SaifSabban/N64-WirelessControllerMod/Extra/Images/5.jpg

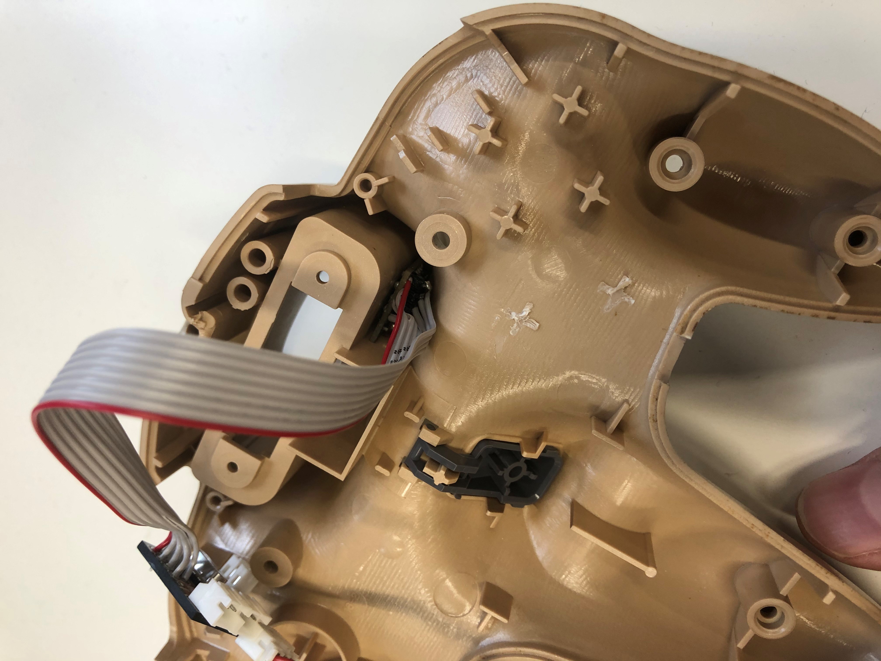
Extra/Images/5.jpg
