SaifSabban/N64-WirelessControllerMod/Extra/Images/6.jpg

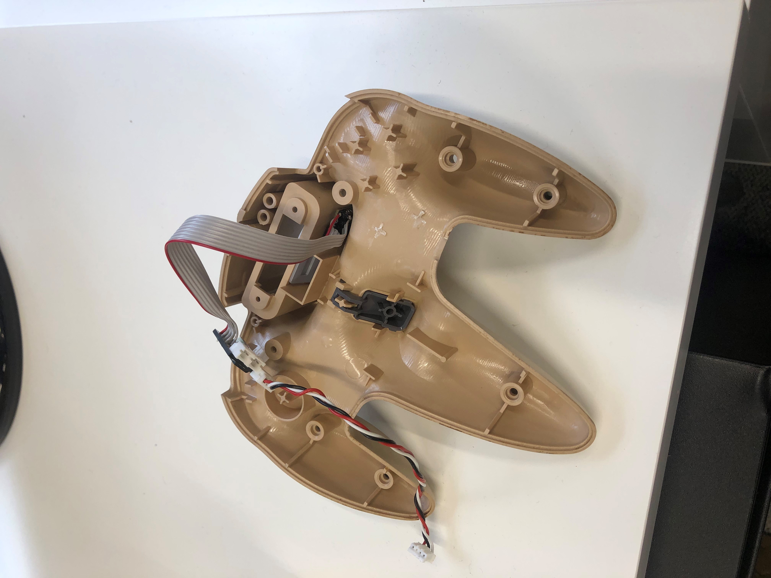
Extra/Images/6.jpg
