SaifSabban/N64-WirelessControllerMod/Extra/Images/10.jpg

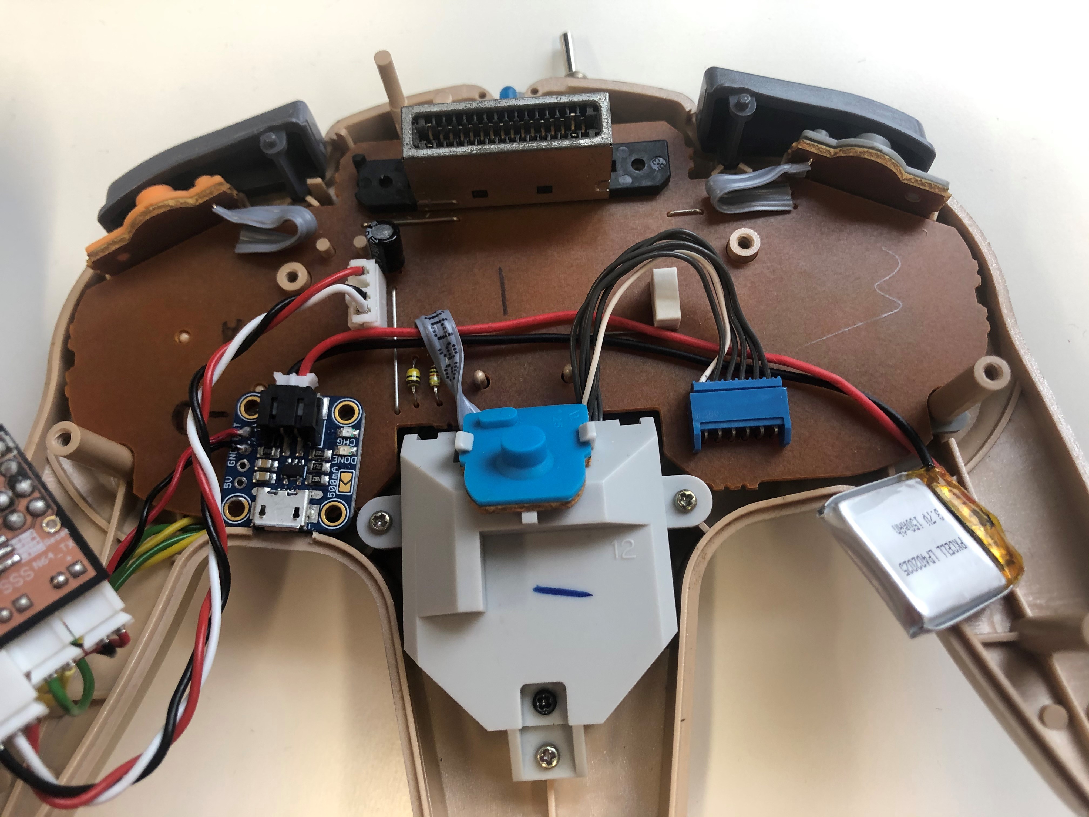
Extra/Images/10.jpg
