SaifSabban/N64-WirelessControllerMod/Extra/Images/12.jpg

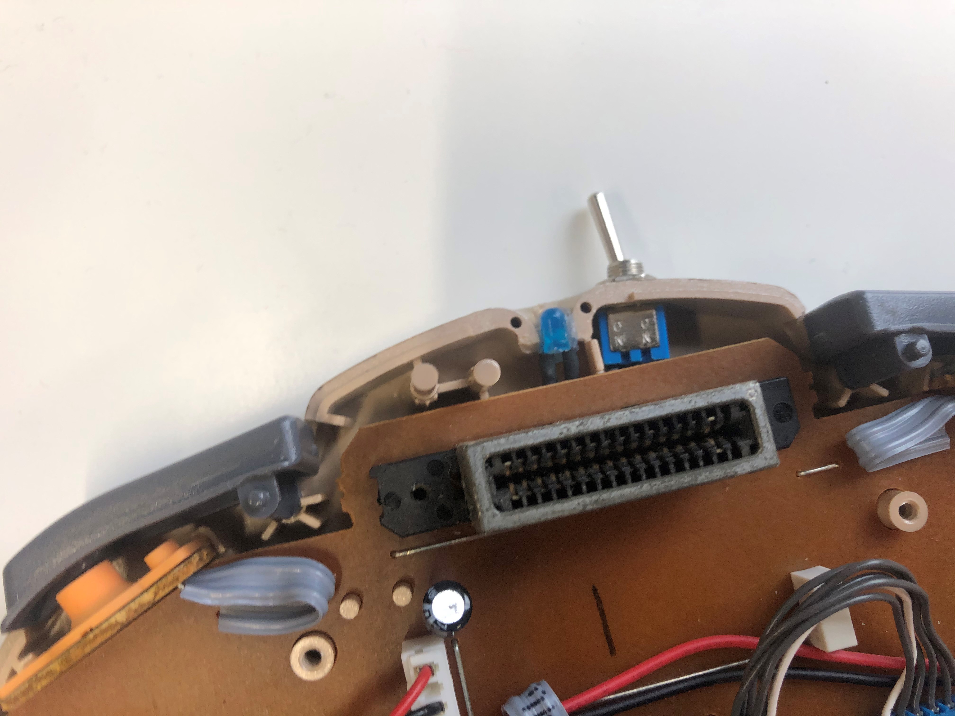
Extra/Images/12.jpg
