SaifSabban/N64-WirelessControllerMod/Extra/Images/13.jpg

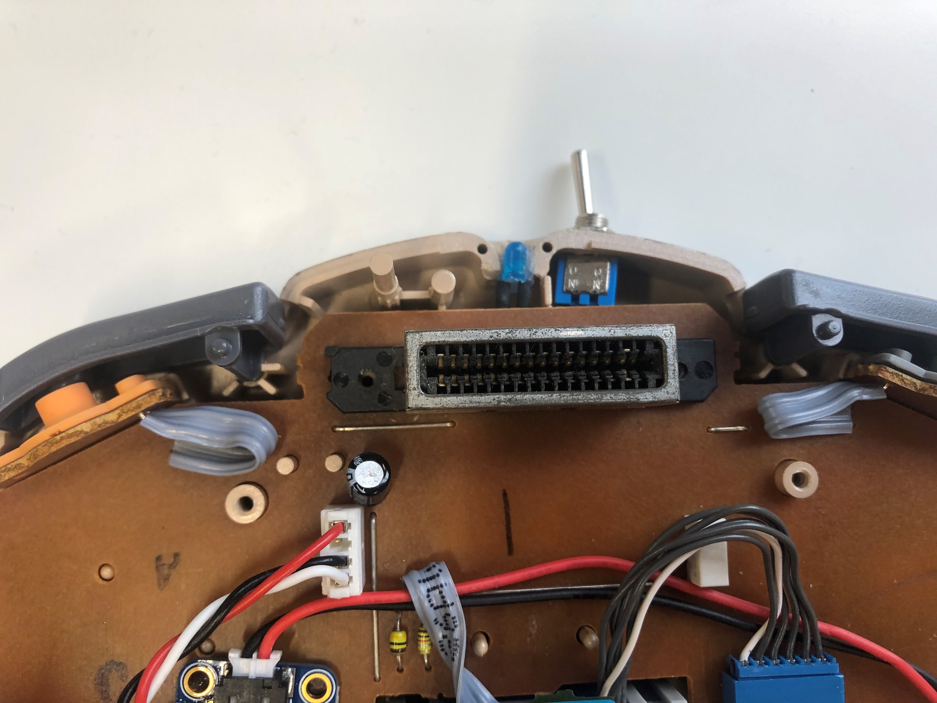
Extra/Images/13.jpg
