SaifSabban/N64-WirelessControllerMod/Extra/Images/14.jpg

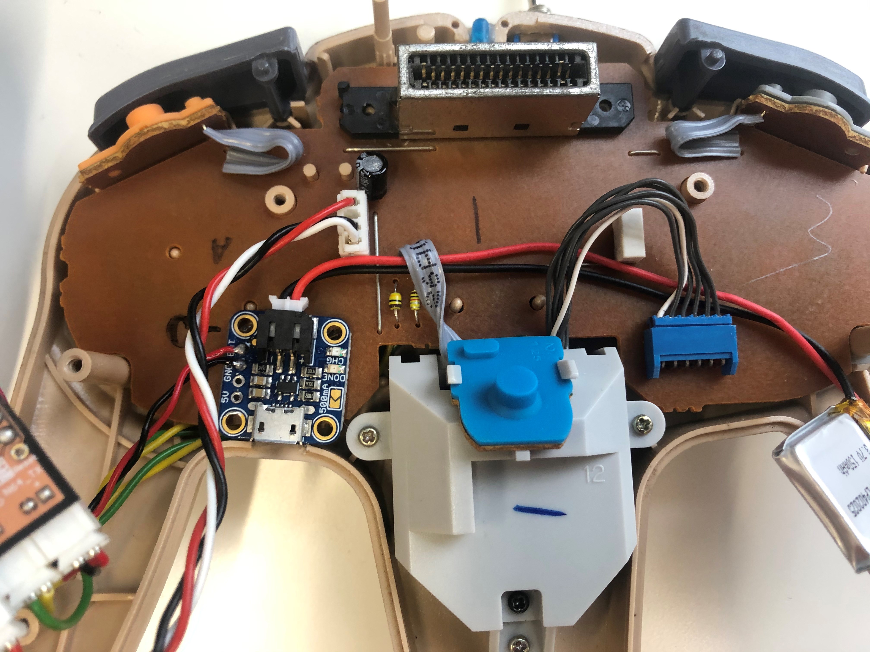
Extra/Images/14.jpg
