SaifSabban/N64-WirelessControllerMod/Extra/Images/17.jpg

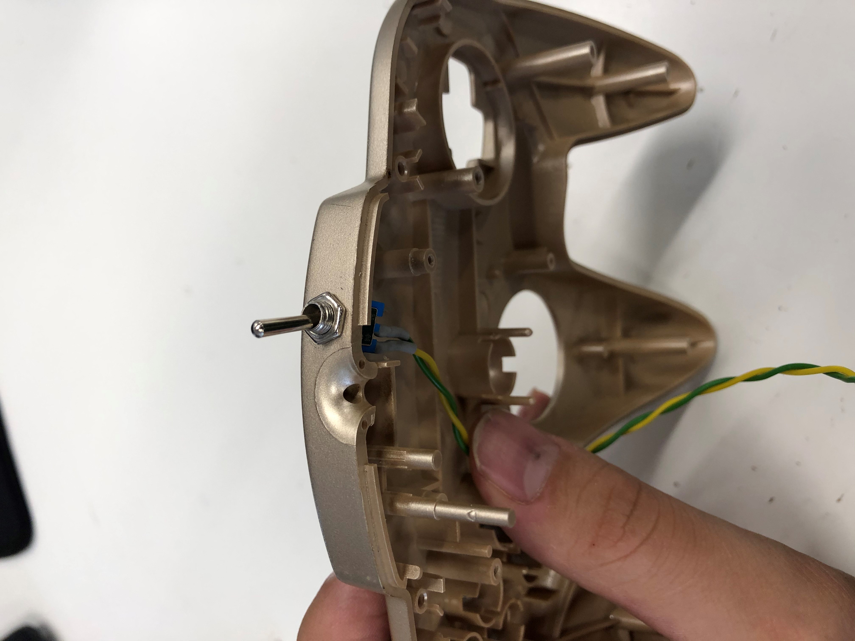
Extra/Images/17.jpg
