SaifSabban/N64-WirelessControllerMod/Extra/Images/19.jpg

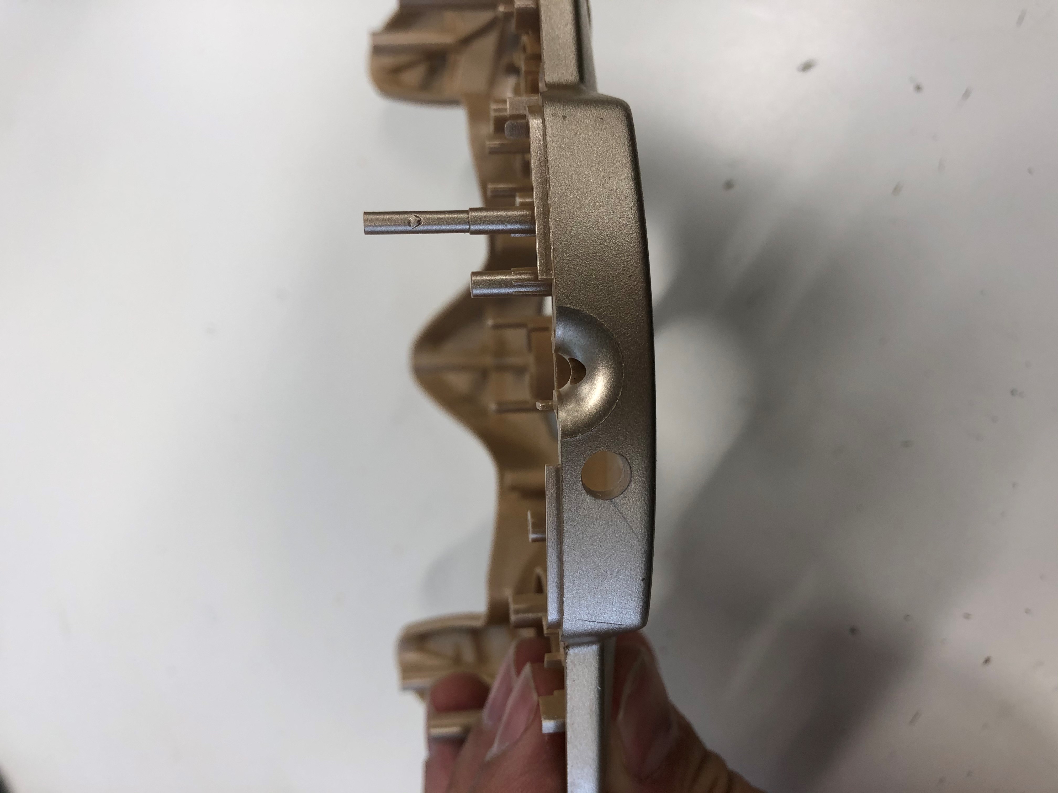
Extra/Images/19.jpg
