SaifSabban/N64-WirelessControllerMod/Extra/Images/20.jpg

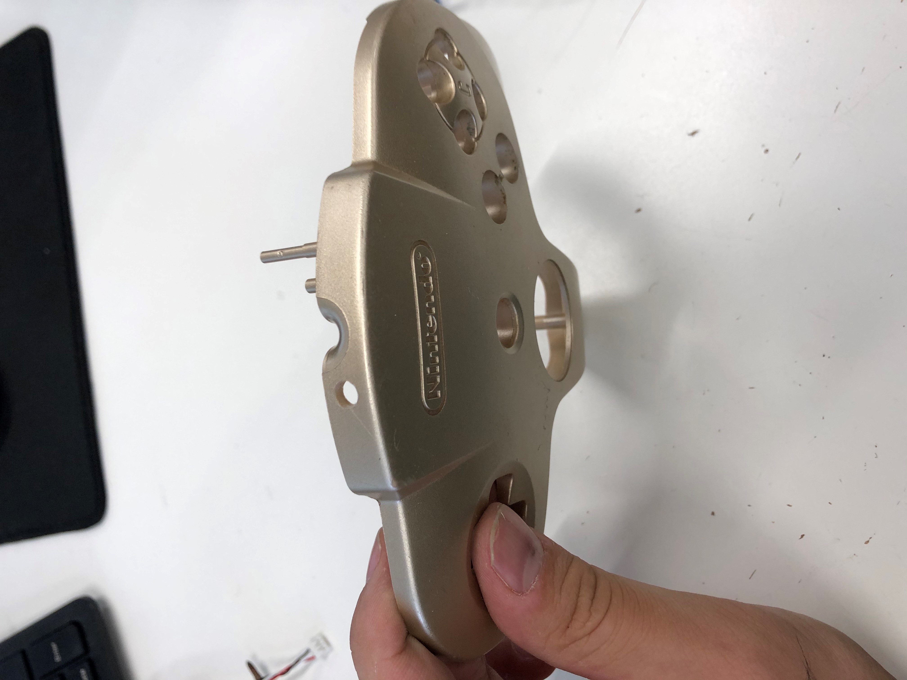
Extra/Images/20.jpg
