SaifSabban/N64-WirelessControllerMod/Extra/Images/21.jpg

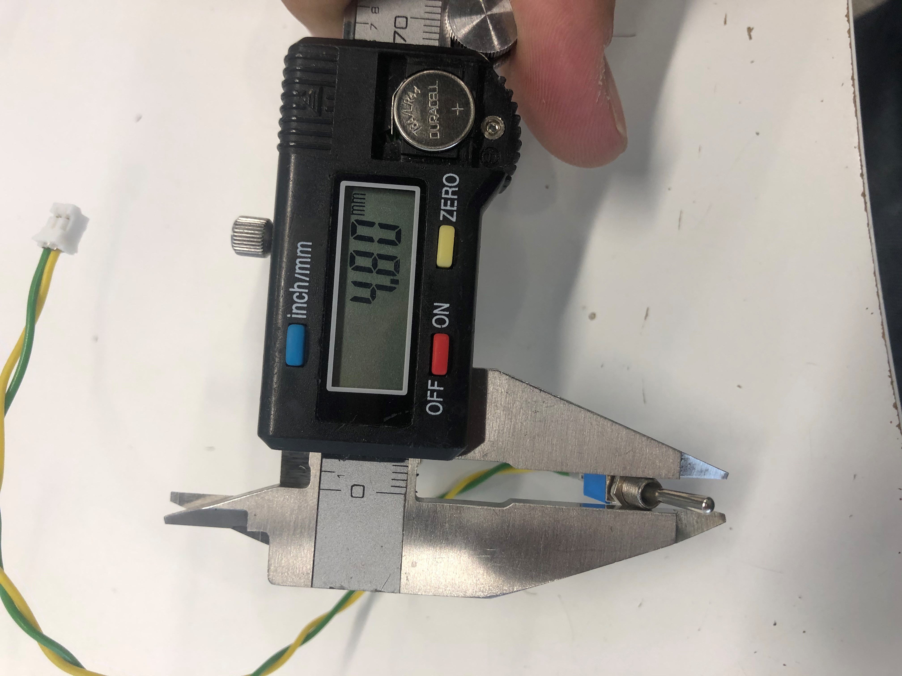
Extra/Images/21.jpg
