SaifSabban/N64-WirelessControllerMod/Extra/Images/23.jpg

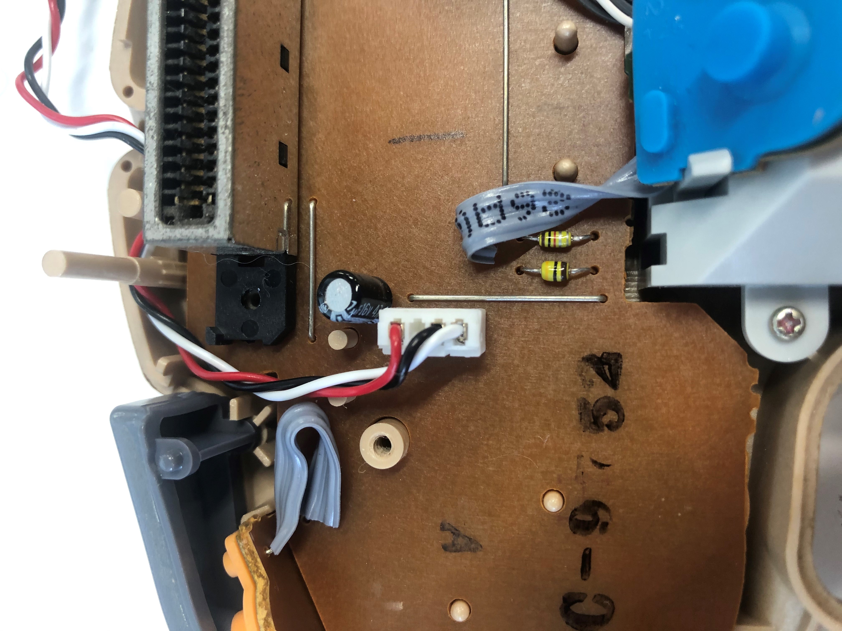
Extra/Images/23.jpg
