SaifSabban/N64-WirelessControllerMod/Extra/Micro-Lipo-Charger/adafruit_products_microlipo.png

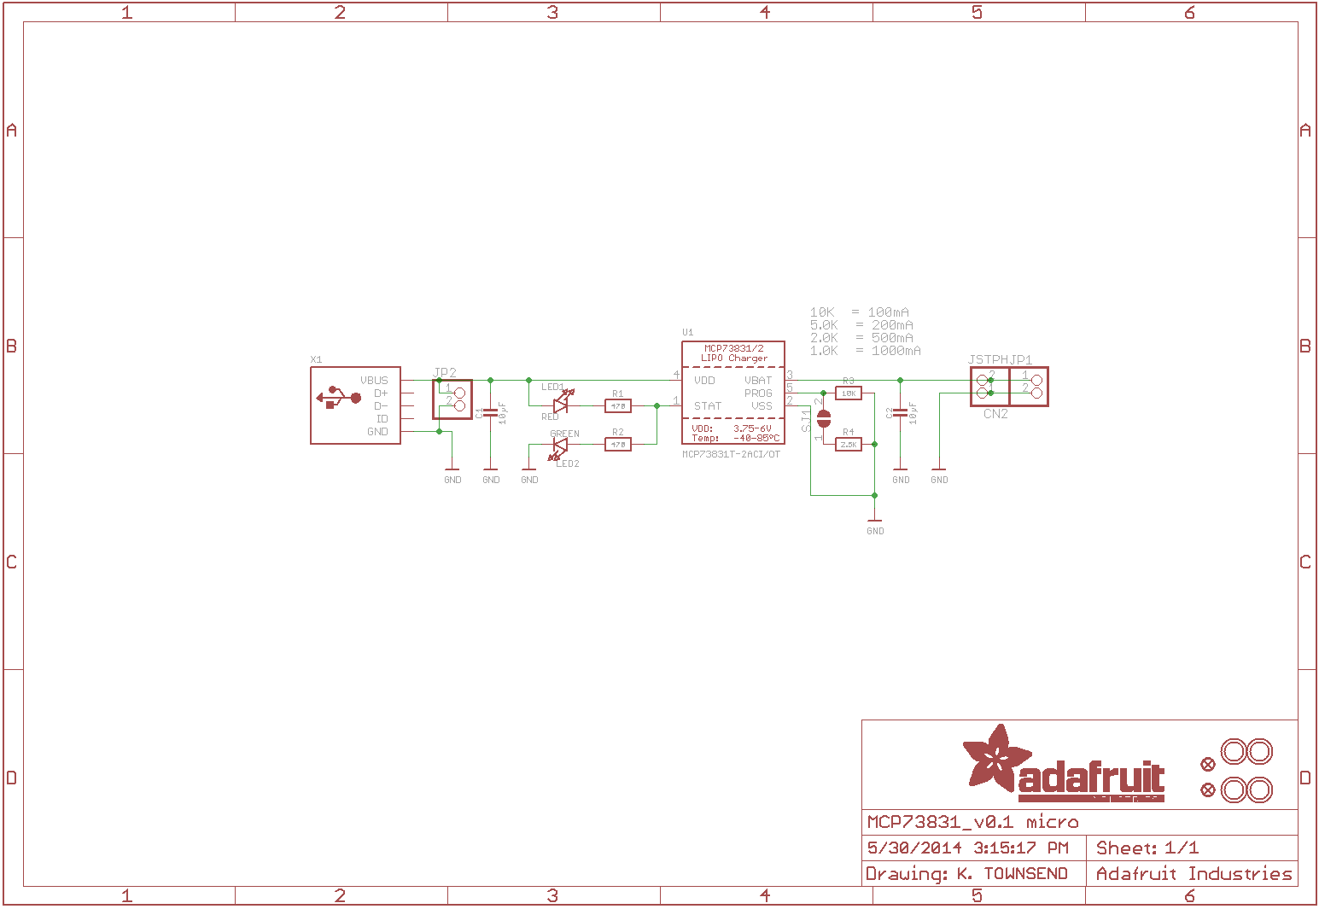
Extra/Micro-Lipo-Charger/adafruit_products_microlipo.png
